luweixuancl/Acode_test/src/web_portal.cpp

#include "web_portal.h"
#include "app_ipc.h"
#include "config.h"
#include "gps_service.h"
#include "ntp_server.h"
#include <ArduinoJson.h>
#include <WiFi.h>
#include <esp_system.h>
#include <math.h>
#include <time.h>

namespace {

String jsonSafeSsid(const String& ssid) {
  const uint8_t* p = reinterpret_cast<const uint8_t*>(ssid.c_str());
  const size_t n = ssid.length();
  bool utf8 = true;
  for (size_t i = 0; i < n;) {
    const uint8_t c = p[i];
    if (c < 0x80) {
      ++i;
      continue;
    }
    size_t need = 0;
    if ((c & 0xE0) == 0xC0) {
      need = 2;
    } else if ((c & 0xF0) == 0xE0) {
      need = 3;
    } else if ((c & 0xF8) == 0xF0) {
      need = 4;
    } else {
      utf8 = false;
      break;
    }
    if (i + need > n) {
      utf8 = false;
      break;
    }
    for (size_t k = 1; k < need; ++k) {
      if ((p[i + k] & 0xC0) != 0x80) {
        utf8 = false;
        break;
      }
    }
    if (!utf8) {
      break;
    }
    i += need;
  }
  if (utf8) {
    return ssid;
  }
  String hex;
  hex.reserve(n * 2 + 4);
  hex = "hex:";
  for (size_t i = 0; i < n; ++i) {
    char b[3];
    snprintf(b, sizeof(b), "%02X", p[i]);
    hex += b;
  }
  return hex;
}

}  // namespace

void WebPortal::begin(WifiManager* wifi, GpsService* gps, NtpServer* ntp) {
  wifi_ = wifi;
  gps_ = gps;
  ntp_ = ntp;
  if (started_) {
    return;
  }

  const char* hdrs[] = {"Cookie"};
  server_.collectHeaders(hdrs, 1);

  server_.on("/", HTTP_GET, [this]() { handleRoot(); });
  server_.on("/setup", HTTP_GET, [this]() { handleSetupEntry(); });
  server_.on("/setup/", HTTP_GET, [this]() { handleSetupEntry(); });
  server_.on("/cfg", HTTP_GET, [this]() { handleSetup(); });
  server_.on("/cfg/", HTTP_GET, [this]() { handleSetup(); });
  server_.on("/login", HTTP_GET, [this]() { sendLoginPage(""); });
  server_.on("/login", HTTP_POST, [this]() { handleLogin(); });
  server_.on("/logout", HTTP_GET, [this]() { handleLogout(); });
  server_.on("/scan", HTTP_GET, [this]() { handleScan(); });
  server_.on("/save", HTTP_POST, [this]() { handleSave(); });
  server_.on("/status", HTTP_GET, [this]() { handleStatus(); });
  server_.on("/metrics", HTTP_GET, [this]() { handleMetrics(); });
  server_.onNotFound([this]() {
    sendNoCache();
    const bool apUp = (WiFi.getMode() == WIFI_AP || WiFi.getMode() == WIFI_AP_STA);
    // Captive probes must not land on settings HTML. SoftAP → login; STA → status.
    if (apUp && wifi_ && !wifi_->isStaConnected()) {
      server_.sendHeader("Location", "/login", true);
      server_.send(302, "text/plain", "");
      return;
    }
    server_.sendHeader("Location", "/", true);
    server_.send(302, "text/plain", "");
  });
  server_.begin();
  started_ = true;
  Serial.println("HTTP on :80  (/ and /status /metrics open; /cfg needs login)");
}

void WebPortal::loop() {
  if (started_) {
    server_.handleClient();
  }
}

bool WebPortal::consumeConnectRequest(String& ssid, String& pass) {
  if (!pendingConnect_) {
    return false;
  }
  pendingConnect_ = false;
  ssid = pendingSsid_;
  pass = pendingPass_;
  return true;
}

String WebPortal::writePassword() const {
  String expect;
  if (settingsLock(pdMS_TO_TICKS(100))) {
    expect = effectiveWebWritePassword(gSettings);
    settingsUnlock();
  } else {
    expect = derivedSoftApPassword();
  }
  if (expect.isEmpty()) {
    expect = derivedSoftApPassword();
  }
  return expect;
}

void WebPortal::sendNoCache() {
  server_.sendHeader("Cache-Control", "no-store, no-cache, must-revalidate, max-age=0");
  server_.sendHeader("Pragma", "no-cache");
}

void WebPortal::issueSession() {
  char tok[17];
  snprintf(tok, sizeof(tok), "%08x%08x", static_cast<unsigned>(esp_random()),
           static_cast<unsigned>(esp_random()));
  sessionToken_ = tok;
  sessionUntilMs_ = millis() + 30UL * 60UL * 1000UL;
  String cookie = String("ntp_sess=") + sessionToken_ +
                  "; Path=/; Max-Age=1800; HttpOnly; SameSite=Lax";
  server_.sendHeader("Set-Cookie", cookie);
}

bool WebPortal::sessionCookieOk() {
  if (sessionToken_.isEmpty() || sessionUntilMs_ == 0) {
    return false;
  }
  if (static_cast<int32_t>(millis() - sessionUntilMs_) >= 0) {
    return false;
  }
  const String cookie = server_.header("Cookie");
  const String needle = String("ntp_sess=") + sessionToken_;
  const int pos = cookie.indexOf(needle);
  if (pos < 0) {
    return false;
  }
  if (pos > 0) {
    const char prev = cookie[pos - 1];
    if (prev != ' ' && prev != ';') {
      return false;
    }
  }
  const int end = pos + needle.length();
  if (end < static_cast<int>(cookie.length())) {
    const char next = cookie[end];
    if (next != ';' && next != ' ') {
      return false;
    }
  }
  return true;
}

bool WebPortal::requireSession(bool htmlLogin) {
  if (sessionCookieOk()) {
    return true;
  }
  if (htmlLogin && server_.method() == HTTP_GET) {
    sendLoginPage("");
    return false;
  }
  sendNoCache();
  server_.send(401, "text/plain", "Unauthorized");
  return false;
}

void WebPortal::sendLoginPage(const char* err) {
  sendNoCache();
  String body;
  body += F("<h1>NTP 设置登录</h1>"
            "<div class='card'>"
            "<p>输入配置口令后才能进入设置。口令默认与 SoftAP 相同"
            "（串口 <code>SoftAP default pass=</code> 或 OLED）。"
            "登录后设置页不再要求填写写口令。</p>");
  if (err && err[0]) {
    body += F("<p class='bad'>");
    body += err;
    body += F("</p>");
  }
  body += F("<form method='POST' action='/login'>"
            "<label>配置口令</label>"
            "<input name='password' type='password' autocomplete='current-password' autofocus>"
            "<button type='submit'>进入设置</button>"
            "</form></div>"
            "<p><a href='/'>返回状态</a></p>");
  server_.send(200, "text/html", buildPage("NTP 登录", body));
}

void WebPortal::handleLogin() {
  const String pass = server_.arg("password");
  const String expect = writePassword();
  if (!pass.isEmpty() && !expect.isEmpty() && pass == expect) {
    issueSession();
    sendNoCache();
    server_.sendHeader("Location", "/cfg", true);
    server_.send(302, "text/plain", "");
    return;
  }
  sendLoginPage("口令错误");
}

void WebPortal::handleLogout() {
  sessionToken_ = "";
  sessionUntilMs_ = 0;
  sendNoCache();
  server_.sendHeader("Set-Cookie", "ntp_sess=; Path=/; Max-Age=0");
  server_.sendHeader("Location", "/login", true);
  server_.send(302, "text/plain", "");
}

void WebPortal::handleSetupEntry() {
  sendNoCache();
  if (sessionCookieOk()) {
    server_.sendHeader("Location", "/cfg", true);
    server_.send(302, "text/plain", "");
    return;
  }
  sendLoginPage("");
}

String WebPortal::buildPage(const String& title, const String& body, bool refresh) const {
  String html;
  html.reserve(body.length() + 700);
  html += F("<!DOCTYPE html><html><head><meta charset='utf-8'>"
            "<meta name='viewport' content='width=device-width,initial-scale=1'>"
            "<meta http-equiv='Cache-Control' content='no-store'>");
  if (refresh) {
    html += F("<meta http-equiv='refresh' content='2'>");
  }
  html += F("<title>");
  html += title;
  html += F("</title><style>"
            "body{font-family:sans-serif;max-width:480px;margin:24px auto;padding:0 12px;background:#0f172a;color:#e2e8f0}"
            "h1{font-size:1.25rem}button,input,select{font-size:1rem;padding:8px;margin:6px 0;width:100%;box-sizing:border-box}"
            "button{background:#38bdf8;border:0;border-radius:8px;color:#0f172a;font-weight:700}"
            "a{color:#38bdf8}.card{background:#1e293b;padding:16px;border-radius:12px;margin:12px 0}"
            ".row{display:flex;justify-content:space-between;gap:12px;padding:6px 0;border-bottom:1px solid #334155}"
            ".row:last-child{border-bottom:0}.k{color:#94a3b8}.v{font-weight:700;text-align:right}"
            ".ok{color:#4ade80}.warn{color:#fbbf24}.bad{color:#f87171}"
            "</style></head><body>");
  html += body;
  html += F("</body></html>");
  return html;
}

void WebPortal::handleRoot() {
  // `/` is always the read-only status page (SoftAP and STA). Settings live at /cfg
  // after login — never serve that HTML here (also busts old cached SoftAP `/` setup).
  sendNoCache();

  // Static shell; live values filled by JS polling /status (no full-page refresh).
  String body = F(
      "<h1>GNSS NTP 状态</h1><p><a href='/cfg'>设置（需登录）</a></p>"
      "<div class='card'>"
      "<div class='row'><span class='k'>NTP</span><span class='v' id='ntpState'>--</span></div>"
      "<div class='row'><span class='k'>时钟</span><span class='v' id='clk'>--</span></div>"
      "<div class='row'><span class='k'>Residual</span><span class='v' id='res'>--</span></div>"
      "<div class='row'><span class='k'>频偏</span><span class='v' id='freq'>--</span></div>"
      "<div class='row'><span class='k'>Root 质量</span><span class='v' id='qual'>--</span></div>"
      "<div class='row'><span class='k'>策略</span><span class='v' id='apol'>--</span></div>"
      "<div class='row'><span class='k'>守时上限</span><span class='v' id='hold'>--</span></div>"
      "<div class='row'><span class='k'>守时中</span><span class='v' id='holdms'>--</span></div>"
      "<div class='row'><span class='k'>Stratum</span><span class='v' id='stratum'>--</span></div>"
      "<div class='row'><span class='k'>Leap</span><span class='v' id='li'>--</span></div>"
      "<div class='row'><span class='k'>RefID</span><span class='v' id='refId'>GPSS</span></div>"
      "<div class='row'><span class='k'>查询次数</span><span class='v' id='ntpReq'>--</span></div>"
      "<div class='row'><span class='k'>UTC</span><span class='v' id='utc'>--</span></div>"
      "<div class='row'><span class='k'>本地</span><span class='v' id='local'>--</span></div>"
      "</div>"
      "<div class='card'>"
      "<div class='row'><span class='k'>GPS 锁定</span><span class='v' id='fix'>--</span></div>"
      "<div class='row'><span class='k'>搜星</span><span class='v' id='sats'>--</span></div>"
      "<div class='row'><span class='k'>HDOP</span><span class='v' id='hdop'>--</span></div>"
      "<div class='row'><span class='k'>PPS</span><span class='v' id='pps'>--</span></div>"
      "<div class='row'><span class='k'>NMEA 龄</span><span class='v' id='age'>--</span></div>"
      "<div class='row'><span class='k'>时间有效</span><span class='v' id='tvalid'>--</span></div>"
      "<div class='row'><span class='k'>经纬度</span><span class='v' id='ll'>--</span></div>"
      "</div>"
      "<div class='card'>"
      "<div class='row'><span class='k'>已服务</span><span class='v' id='served'>--</span></div>"
      "<div class='row'><span class='k'>限流 RATE</span><span class='v' id='rate'>--</span></div>"
      "<div class='row'><span class='k'>DENY</span><span class='v' id='deny'>--</span></div>"
      "<div class='row'><span class='k'>静默丢弃</span><span class='v' id='drop'>--</span></div>"
      "<div class='row'><span class='k'>ACL 拒绝</span><span class='v' id='adny'>--</span></div>"
      "<div class='row'><span class='k'>活跃客户端</span><span class='v' id='clients'>--</span></div>"
      "<div class='row'><span class='k'>ACL 模式</span><span class='v' id='aclm'>--</span></div>"
      "</div>"
      "<div class='card'>"
      "<div class='row'><span class='k'>IP</span><span class='v' id='ip'>--</span></div>"
      "<div class='row'><span class='k'>SSID</span><span class='v' id='ssid'>--</span></div>"
      "<div class='row'><span class='k'>RSSI</span><span class='v' id='rssi'>--</span></div>"
      "<div class='row'><span class='k'>MAC</span><span class='v' id='mac'>--</span></div>"
      "<div class='row'><span class='k'>运行</span><span class='v' id='up'>--</span></div>"
      "<div class='row'><span class='k'>内存</span><span class='v' id='heap'>--</span></div>"
      "<div class='row'><span class='k'>温度</span><span class='v' id='temp'>--</span></div>"
      "</div>"
      "<p style='color:#64748b'>自动更新 1 Hz · JSON: <a href='/status'>/status</a> · 指标: <a href='/metrics'>/metrics</a></p>"
      "<script>"
      "function pad(n){return n<10?'0'+n:''+n}"
      "function fmt(epoch,tz){"
      " if(!epoch)return '--';"
      " const d=new Date((epoch+tz*3600)*1000);"
      " return d.getUTCFullYear()+'-'+pad(d.getUTCMonth()+1)+'-'+pad(d.getUTCDate())+' '"
      "  +pad(d.getUTCHours())+':'+pad(d.getUTCMinutes())+':'+pad(d.getUTCSeconds())}"
      "function fmtUp(s){"
      " if(s==null)return '--';"
      " const d=Math.floor(s/86400),h=Math.floor(s%86400/3600),m=Math.floor(s%3600/60),x=s%60;"
      " return (d?d+'d ':'')+pad(h)+':'+pad(m)+':'+pad(x)}"
      "function setCls(el,c){el.className='v '+(c||'')}"
      "async function tick(){"
      " try{"
      "  const r=await fetch('/status'); const j=await r.json();"
      "  const g=j.gps||{}, n=j.ntp||{}, c=j.clock||{};"
      "  const have=!!n.synced, pps=!!g.ppsFresh, s1=!!n.stratum1Ready;"
      "  const st=document.getElementById('ntpState');"
      "  st.textContent=s1?'Stratum 1 就绪':(have?'降级/守时':'未同步');"
      "  setCls(st,s1?'ok':(have?'warn':'bad'));"
      "  document.getElementById('clk').textContent=c.state||'--';"
      "  document.getElementById('res').textContent=(c.residualMs!=null)?(c.residualMs+' ms'):'--';"
      "  document.getElementById('freq').textContent=(c.freqPpm!=null)"
      "    ?(Number(c.freqPpm).toFixed(2)+' ppm'):'--';"
      "  document.getElementById('qual').textContent=(g.qualityMs!=null)?(g.qualityMs+' ms'):'--';"
      "  document.getElementById('apol').textContent=j.anomalyLabel||'--';"
      "  document.getElementById('hold').textContent=(j.holdoverSec!=null)?(j.holdoverSec+' s'):'--';"
      "  const hm=document.getElementById('holdms');"
      "  hm.textContent=(c.holdoverMs>0)?(Math.round(c.holdoverMs/1000)+' s'):'-';"
      "  setCls(hm,c.holdoverMs>0?'warn':'');"
      "  document.getElementById('stratum').textContent=(n.stratum!=null)?n.stratum:'--';"
      "  const li=document.getElementById('li');"
      "  li.textContent=(n.li!=null)?('LI='+n.li):'--'; setCls(li,n.li===0?'ok':'warn');"
      "  document.getElementById('refId').textContent=n.refId||'GPSS';"
      "  document.getElementById('ntpReq').textContent=(n.requests!=null)?n.requests:'--';"
      "  const tz=j.tzHours||0;"
      "  document.getElementById('utc').textContent=fmt(g.utcEpoch,0);"
      "  document.getElementById('local').textContent=fmt(g.utcEpoch,tz)"
      "    +' (UTC'+(tz>=0?'+':'')+tz+')';"
      "  const fx=document.getElementById('fix');"
      "  fx.textContent=g.fix?'是':'否'; setCls(fx,g.fix?'ok':'bad');"
      "  document.getElementById('sats').textContent=(g.satellites!=null)?g.satellites:'--';"
      "  document.getElementById('hdop').textContent=(g.hdop!=null)?Number(g.hdop).toFixed(1):'--';"
      "  const pp=document.getElementById('pps');"
      "  pp.textContent=(pps?'正常':'无')+' ('+(g.ppsCount||0)+')'; setCls(pp,pps?'ok':'bad');"
      "  document.getElementById('age').textContent=(g.ageMs!=null)?(g.ageMs+' ms'):'--';"
      "  const tv=document.getElementById('tvalid');"
      "  tv.textContent=g.timeValid?'有效':'无效'; setCls(tv,g.timeValid?'ok':'bad');"
      "  document.getElementById('ll').textContent=g.fix"
      "    ?(Number(g.lat).toFixed(5)+', '+Number(g.lon).toFixed(5)):'--';"
      "  document.getElementById('served').textContent=(n.served!=null)?n.served:'--';"
      "  document.getElementById('rate').textContent=(n.rateLimited!=null)?n.rateLimited:'--';"
      "  document.getElementById('deny').textContent=(n.denied!=null)?n.denied:'--';"
      "  document.getElementById('drop').textContent=(n.dropped!=null)?n.dropped:'--';"
      "  document.getElementById('adny').textContent=(n.aclDenied!=null)?n.aclDenied:'--';"
      "  document.getElementById('clients').textContent=(n.clients!=null)?n.clients:'--';"
      "  document.getElementById('aclm').textContent=(j.ntpAclLabel||'--')"
      "    +' ('+((j.ntpAcl&&j.ntpAcl.length)||0)+')';"
      "  document.getElementById('ip').textContent=j.ip||'--';"
      "  document.getElementById('ssid').textContent=j.ssid||'--';"
      "  document.getElementById('rssi').textContent=(j.rssi!=null)?(j.rssi+' dBm'):'--';"
      "  document.getElementById('mac').textContent=j.mac||'--';"
      "  document.getElementById('up').textContent=fmtUp(j.uptimeSec);"
      "  const hb=Math.round((j.freeHeap||0)/1024), hmn=Math.round((j.minFreeHeap||0)/1024);"
      "  const he=document.getElementById('heap');"
      "  he.textContent=hb+' KB (min '+hmn+')'; setCls(he,hb<20480?'bad':'');"
      "  const tp=document.getElementById('temp');"
      "  tp.textContent=(c.tempC!=null)?(Number(c.tempC).toFixed(1)+'°C · '"
      "    +(c.tempComp?('补偿 '+Number(c.tempCorrPpm||0).toFixed(2)+' ppm'):'补偿关')):'--';"
      " }catch(e){}"
      "}"
      "tick(); setInterval(tick,1000);"
      "</script>");

  server_.send(200, "text/html", buildPage("NTP 状态", body, false));
}

void WebPortal::handleSetup() {
  if (!requireSession(true)) {
    return;
  }
  uint8_t apol = 0;
  uint8_t aclm = 0;
  bool tcmp = false;
  int16_t tcpc = CLK_TEMP_COEFF_CENTI;
  uint32_t ooffMin = OLED_IDLE_OFF_DEFAULT_MS / 60000;
  String aclLines;
  String savedSsid;
  bool haveSaved = false;
  if (settingsLock(pdMS_TO_TICKS(50))) {
    apol = static_cast<uint8_t>(gSettings.anomalyPolicy);
    aclm = static_cast<uint8_t>(gSettings.ntpAclMode);
    tcmp = gSettings.tempComp;
    tcpc = gSettings.tempCoeffCenti;
    ooffMin = gSettings.oledIdleOffMs / 60000;
    for (uint8_t i = 0; i < gSettings.ntpAclCount && i < NTP_ACL_MAX_ENTRIES; ++i) {
      if (i) {
        aclLines += '\n';
      }
      aclLines += gSettings.ntpAcl[i].toString();
    }
    savedSsid = gSettings.wifiSsid;
    haveSaved = !savedSsid.isEmpty();
    settingsUnlock();
  }
  String body;
  body.reserve(5600);
  body += F("<!-- ntp-cfg-v2 -->"
            "<h1>NTP 设置</h1><p><a href='/'>返回状态</a> · <a href='/logout'>退出</a></p>");
  if (haveSaved) {
    body += F("<div class='card'><h2 style='font-size:1rem;margin:0 0 8px'>已保存的 WiFi</h2><p>SSID: <b>");
    body += savedSsid;
    body += F("</b></p>"
              "<p style='color:#64748b;font-size:.85rem'>固件更新后会自动重连；无需重新输入 WiFi 密码。"
              "仅当路由器改密或换热点时才需要下方重新配网。</p>"
              "<button type='button' onclick='reconnectSaved()'>使用已保存网络重连</button>"
              "<p id='rmsg'></p></div>");
  }
  body += F("<div class='card'><h2 style='font-size:1rem;margin:0 0 8px'>GPS 异常策略</h2>"
            "<select id='apol'>"
            "<option value='0'>立即拒绝授时 (Refuse)</option>"
            "<option value='1'>短时守时 Holdover 30s</option>"
            "<option value='2'>长时守时 Holdover 5min</option>"
            "</select>"
            "<button type='button' onclick='savePolicy()'>保存策略</button>"
            "<p id='pmsg'></p></div>");
  body += F("<div class='card'><h2 style='font-size:1rem;margin:0 0 8px'>NTP ACL 白名单</h2>"
            "<p style='color:#64748b;font-size:.85rem'>默认 Off。开启 AllowList 后仅列出的 IPv4 可取时"
            "（最多 8 条；未命中静默丢弃；空列表=拒绝全部）。</p>"
            "<label>模式</label><select id='aclm'>"
            "<option value='0'>Off（不限制）</option>"
            "<option value='1'>AllowList</option>"
            "</select>"
            "<label>允许的 IP（每行一个）</label>"
            "<textarea id='acllist' rows='5' style='width:100%;font-family:monospace'></textarea>"
            "<button type='button' onclick='saveAcl()'>保存 ACL</button>"
            "<p id='amsg'></p></div>");
  body += F("<div class='card'><h2 style='font-size:1rem;margin:0 0 8px'>晶振温度补偿</h2>"
            "<p style='color:#64748b;font-size:.85rem'>默认关。用片上温度对 Holdover 外推做一阶 "
            "ppm/°C 修正（相对最近 PPS 估频时的温度）。系数可改，默认 -0.50。</p>"
            "<label>模式</label><select id='tcmp'>"
            "<option value='0'>Off</option>"
            "<option value='1'>On</option>"
            "</select>"
            "<label>系数 ppm/°C</label>"
            "<input id='tcpc' type='number' step='0.01'>"
            "<button type='button' onclick='saveTemp()'>保存温度补偿</button>"
            "<p id='tmsg'></p></div>");
  body += F("<div class='card'><h2 style='font-size:1rem;margin:0 0 8px'>屏幕息屏</h2>"
            "<p style='color:#64748b;font-size:.85rem'>无旋钮操作达到该时长后关闭 OLED 面板（防烧屏）。"
            "旋转/单击旋钮唤醒，首个动作仅唤醒不导航；系统提示（OK IP 等）会自动亮屏。0 = 常亮。</p>"
            "<label>息屏时间</label><select id='ooff'>"
            "<option value='0'>常亮（不息屏）</option>"
            "<option value='1'>1 分钟</option>"
            "<option value='5'>5 分钟</option>"
            "<option value='10'>10 分钟（默认）</option>"
            "<option value='30'>30 分钟</option>"
            "</select>"
            "<button type='button' onclick='saveScreen()'>保存息屏</button>"
            "<p id='smsg'></p></div>");
  body += F("<div class='card'><h2 style='font-size:1rem;margin:0 0 8px'>WiFi 配网</h2>"
            "<p>扫描热点，选择 SSID，输入密码后连接。</p>"
            "<button type='button' onclick='scan()'>扫描 WiFi</button>"
            "<label>SSID</label><select id='ssid'></select>"
            "<label>Password</label><input id='pass' type='password'>"
            "<button type='button' onclick='saveWifi()'>连接</button>"
            "<p id='msg'></p></div>");
  body += F("<script>"
            "async function sleep(ms){return new Promise(r=>setTimeout(r,ms));}"
            "async function postSave(obj){"
            " const r=await fetch('/save',{method:'POST',credentials:'same-origin',"
            "  headers:{'Content-Type':'application/json'},body:JSON.stringify(obj)});"
            " if(r.status===401){location.href='/login';return '';}"
            " return r.text();}"
            "async function scan(){"
            " try{"
            " document.getElementById('msg').textContent='Scanning...';"
            " let j=null;"
            " for(let i=0;i<50;i++){"
            "  const r=await fetch('/scan',{credentials:'same-origin'});"
            "  if(r.status===401){location.href='/login';return;}"
            "  if(r.status===202){await sleep(250);continue;}"
            "  if(!r.ok){document.getElementById('msg').textContent='Scan failed';return;}"
            "  j=await r.json(); break;"
            " }"
            " if(!j){document.getElementById('msg').textContent='Scan timeout';return;}"
            " const s=document.getElementById('ssid'); s.innerHTML='';"
            " j.forEach(n=>{const o=document.createElement('option');"
            " o.value=n.ssid; o.textContent=n.ssid+' ('+n.rssi+'dBm)'; s.appendChild(o);});"
            " document.getElementById('msg').textContent='Found '+j.length+' networks';"
            " }catch(e){document.getElementById('msg').textContent=String(e);}"
            "}"
            "async function saveWifi(){"
            " try{"
            " const ssid=document.getElementById('ssid').value;"
            " const pass=document.getElementById('pass').value;"
            " document.getElementById('msg').textContent=await postSave({ssid,pass});"
            " }catch(e){document.getElementById('msg').textContent=String(e);}"
            "}"
            "async function reconnectSaved(){"
            " try{"
            "  document.getElementById('rmsg').textContent=await postSave({reconnectSaved:true});"
            " }catch(e){document.getElementById('rmsg').textContent=String(e);}"
            "}"
            "async function savePolicy(){"
            " try{"
            " const anomalyPolicy=parseInt(document.getElementById('apol').value,10);"
            " document.getElementById('pmsg').textContent=await postSave({anomalyPolicy});"
            " }catch(e){document.getElementById('pmsg').textContent=String(e);}"
            "}"
            "async function saveAcl(){"
            " try{"
            " const ntpAclMode=parseInt(document.getElementById('aclm').value,10);"
            " const ntpAcl=document.getElementById('acllist').value.split(/\\r?\\n/)"
            "  .map(s=>s.trim()).filter(s=>s.length>0);"
            " document.getElementById('amsg').textContent=await postSave({ntpAclMode,ntpAcl});"
            " }catch(e){document.getElementById('amsg').textContent=String(e);}"
            "}"
            "async function saveTemp(){"
            " try{"
            " const tempComp=parseInt(document.getElementById('tcmp').value,10)===1;"
            " const tempCoeff=parseFloat(document.getElementById('tcpc').value);"
            " document.getElementById('tmsg').textContent=await postSave({tempComp,tempCoeff});"
            " }catch(e){document.getElementById('tmsg').textContent=String(e);}"
            "}"
            "async function saveScreen(){"
            " try{"
            " const oledIdleMin=parseInt(document.getElementById('ooff').value,10);"
            " document.getElementById('smsg').textContent=await postSave({oledIdleMin});"
            " }catch(e){document.getElementById('smsg').textContent=String(e);}"
            "}"
            "document.getElementById('apol').value='");
  body += String(apol);
  body += F("';"
            "document.getElementById('aclm').value='");
  body += String(aclm);
  body += F("';"
            "document.getElementById('tcmp').value='");
  body += String(tcmp ? 1 : 0);
  body += F("';"
            "document.getElementById('tcpc').value='");
  {
    char buf[16];
    snprintf(buf, sizeof(buf), "%.2f", static_cast<double>(tempCoeffPpmPerC(tcpc)));
    body += buf;
  }
  body += F("';"
            "document.getElementById('ooff').value='");
  body += String(static_cast<unsigned>(ooffMin));
  body += F("';"
            "document.getElementById('acllist').value=");
  // JSON-encode the ACL lines for safe JS string.
  {
    JsonDocument tmp;
    tmp.set(aclLines);
    String enc;
    serializeJson(tmp, enc);
    body += enc;
  }
  body += F(";");
  if (!haveSaved) {
    body += F("scan();");
  }
  body += F("</script>");
  sendNoCache();
  server_.send(200, "text/html", buildPage("NTP 设置", body));
}

void WebPortal::handleScan() {
  if (!requireSession(false)) {
    return;
  }
  if (wifi_ == nullptr) {
    server_.send(503, "application/json", "{\"error\":\"no wifi\"}");
    return;
  }

  // Do not kick STA join or scanDelete() an in-flight OLED harvest.
  if (wifi_->isConnecting() && !wifi_->isStaConnected()) {
    server_.send(202, "application/json", "{\"status\":\"scanning\"}");
    return;
  }
  const bool cacheFresh =
      wifi_->scanState() == WifiScanState::Done && !wifi_->lastScan().empty() &&
      static_cast<int32_t>(millis() - wifi_->lastHarvestMs()) < WIFI_SCAN_CACHE_MS;
  if (!wifi_->isScanRunning() && !wifi_->peekScanDone() && !cacheFresh) {
    if (!wifi_->startScan()) {
      server_.send(503, "application/json", "{\"status\":\"busy\"}");
      return;
    }
  }

  std::vector<WifiNetwork> nets;
  const WifiScanState st = wifi_->pollScan(&nets);
  if (st == WifiScanState::Running) {
    server_.send(202, "application/json", "{\"status\":\"scanning\"}");
    return;
  }
  if (st == WifiScanState::Failed) {
    server_.send(500, "application/json", "{\"status\":\"failed\"}");
    return;
  }

  const std::vector<WifiNetwork>& src = nets.empty() ? wifi_->lastScan() : nets;

  JsonDocument doc;
  JsonArray arr = doc.to<JsonArray>();
  for (const auto& n : src) {
    JsonObject o = arr.add<JsonObject>();
    o["ssid"] = jsonSafeSsid(n.ssid);
    o["rssi"] = n.rssi;
  }
  String out;
  serializeJson(doc, out);
  server_.send(200, "application/json", out);
}

void WebPortal::handleSave() {
  if (!requireSession(false)) {
    return;
  }
  String body = server_.arg("plain");
  JsonDocument doc;
  if (deserializeJson(doc, body)) {
    server_.send(400, "text/plain", "Bad JSON");
    return;
  }

  // Optional password overrides (still require auth above).
  bool touchMgmt = false;
  if (doc["apPassword"].is<const char*>()) {
    String ap = doc["apPassword"].as<const char*>();
    if (ap == "null") {
      ap = "";
    }
    if (!ap.isEmpty() && ap.length() < 8) {
      server_.send(400, "text/plain", "apPassword must be >=8 chars");
      return;
    }
    if (settingsLock(pdMS_TO_TICKS(100))) {
      gSettings.apPassword = ap;
      settingsUnlock();
      touchMgmt = true;
    }
  }
  if (doc["webPassword"].is<const char*>()) {
    String wp = doc["webPassword"].as<const char*>();
    if (wp == "null") {
      wp = "";
    }
    if (settingsLock(pdMS_TO_TICKS(100))) {
      gSettings.webPassword = wp;
      settingsUnlock();
      touchMgmt = true;
    }
  }
  if (touchMgmt && settingsLock(pdMS_TO_TICKS(100))) {
    AppSettings copy = gSettings;
    settingsUnlock();
    gStore.save(copy);
  }

  // Reuse NVS WiFi without retyping password (SoftAP escape / post-OTA).
  if (doc["reconnectSaved"] == true) {
    String ssid;
    String pass;
    if (settingsLock(pdMS_TO_TICKS(200))) {
      ssid = gSettings.wifiSsid;
      pass = gSettings.wifiPass;
      settingsUnlock();
    }
    if (ssid.isEmpty()) {
      server_.send(400, "text/plain", "No saved WiFi");
      return;
    }
    pendingSsid_ = ssid;
    pendingPass_ = pass;
    pendingConnect_ = true;
    server_.send(200, "text/plain", "Reconnecting with saved WiFi...");
    return;
  }

  bool savedPolicy = false;
  if (!doc["anomalyPolicy"].isNull()) {
    const int v = doc["anomalyPolicy"].as<int>();
    if (v >= 0 && v <= static_cast<int>(AnomalyPolicy::HoldoverLong)) {
      AppSettings copy;
      bool locked = false;
      if (settingsLock(pdMS_TO_TICKS(200))) {
        gSettings.anomalyPolicy = static_cast<AnomalyPolicy>(v);
        const uint16_t defHold = anomalyPolicyDefaultHoldoverSec(gSettings.anomalyPolicy);
        if (defHold > 0) {
          gSettings.holdoverSec = defHold;
        }
        if (!doc["holdoverSec"].isNull()) {
          uint16_t hs = doc["holdoverSec"].as<uint16_t>();
          if (hs < 10) hs = 10;
          if (hs > 600) hs = 600;
          gSettings.holdoverSec = hs;
        }
        copy = gSettings;
        settingsUnlock();
        locked = true;
      }
      if (locked) {
        gStore.save(copy);
        savedPolicy = true;
      }
    }
  }

  bool savedAcl = false;
  const bool haveAclMode = !doc["ntpAclMode"].isNull();
  const bool haveAclList = doc["ntpAcl"].is<JsonArray>();
  if (haveAclMode || haveAclList) {
    AppSettings copy;
    bool locked = false;
    if (settingsLock(pdMS_TO_TICKS(200))) {
      if (haveAclMode) {
        const int m = doc["ntpAclMode"].as<int>();
        gSettings.ntpAclMode =
            (m == static_cast<int>(NtpAclMode::AllowList)) ? NtpAclMode::AllowList : NtpAclMode::Off;
      }
      if (haveAclList) {
        JsonArray arr = doc["ntpAcl"].as<JsonArray>();
        uint8_t n = 0;
        for (JsonVariant v : arr) {
          if (n >= NTP_ACL_MAX_ENTRIES) {
            break;
          }
          if (!v.is<const char*>()) {
            continue;
          }
          IPAddress ip;
          if (ip.fromString(v.as<const char*>()) && static_cast<uint32_t>(ip) != 0) {
            gSettings.ntpAcl[n++] = ip;
          }
        }
        gSettings.ntpAclCount = n;
      }
      copy = gSettings;
      settingsUnlock();
      locked = true;
    }
    if (locked) {
      gStore.save(copy);
      savedAcl = true;
    }
  }

  bool savedTemp = false;
  const bool haveTempComp = !doc["tempComp"].isNull();
  const bool haveTempCoeff = !doc["tempCoeff"].isNull();
  if (haveTempComp || haveTempCoeff) {
    AppSettings copy;
    bool locked = false;
    if (settingsLock(pdMS_TO_TICKS(200))) {
      if (haveTempComp) {
        gSettings.tempComp = doc["tempComp"].as<bool>();
      }
      if (haveTempCoeff) {
        float k = doc["tempCoeff"].as<float>();
        if (k < -5.0f) {
          k = -5.0f;
        }
        if (k > 5.0f) {
          k = 5.0f;
        }
        gSettings.tempCoeffCenti = static_cast<int16_t>(lroundf(k * 100.0f));
      }
      copy = gSettings;
      settingsUnlock();
      locked = true;
    }
    if (locked) {
      gStore.save(copy);
      savedTemp = true;
    }
  }

  // OLED idle blanking timeout, in whole minutes (0 = always on).
  bool savedScreen = false;
  if (!doc["oledIdleMin"].isNull()) {
    uint32_t mins = doc["oledIdleMin"].as<uint32_t>();
    if (mins > 60) {
      mins = 60;
    }
    AppSettings copy;
    bool locked = false;
    if (settingsLock(pdMS_TO_TICKS(200))) {
      gSettings.oledIdleOffMs = mins * 60000UL;
      copy = gSettings;
      settingsUnlock();
      locked = true;
    }
    if (locked) {
      gStore.save(copy);
      savedScreen = true;
    }
  }

  // Only touch WiFi creds when ssid is a real JSON string (not missing/null).
  if (doc["ssid"].is<const char*>()) {
    pendingSsid_ = doc["ssid"].as<const char*>();
    pendingPass_ = doc["pass"].is<const char*>() ? String(doc["pass"].as<const char*>()) : String();
    if (pendingSsid_ == "null" || pendingSsid_ == "undefined") {
      pendingSsid_ = "";
    }
    if (!pendingSsid_.isEmpty()) {
      AppSettings copy;
      bool locked = false;
      if (settingsLock(pdMS_TO_TICKS(200))) {
        gSettings.wifiSsid = pendingSsid_;
        gSettings.wifiPass = pendingPass_;
        copy = gSettings;
        settingsUnlock();
        locked = true;
      }
      if (locked) {
        gStore.save(copy);
      }
      pendingConnect_ = true;
      server_.send(200, "text/plain", "Saved. Connecting...");
      return;
    }
  }

  if (savedPolicy || touchMgmt || savedAcl || savedTemp || savedScreen) {
    if (savedTemp) {
      server_.send(200, "text/plain", "Temp comp saved");
    } else if (savedScreen) {
      server_.send(200, "text/plain", "Screen timeout saved");
    } else if (savedAcl) {
      server_.send(200, "text/plain", "ACL saved");
    } else {
      server_.send(200, "text/plain", savedPolicy ? "Policy saved" : "Password updated");
    }
    return;
  }
  server_.send(400, "text/plain", "SSID or anomalyPolicy or ntpAcl required");
}

void WebPortal::handleStatus() {
  JsonDocument doc;
  doc["sta"] = wifi_->isStaConnected();
  doc["ip"] = wifi_->localIp().toString();
  doc["ssid"] = WiFi.SSID();
  doc["rssi"] = WiFi.RSSI();
  doc["mac"] = wifi_->macAddress();
  doc["uptimeSec"] = millis() / 1000;
  doc["freeHeap"] = ESP.getFreeHeap();
  doc["minFreeHeap"] = ESP.getMinFreeHeap();

  AnomalyPolicy apol = AnomalyPolicy::Refuse;
  uint16_t hold = 0;
  String savedSsid;
  NtpAclMode aclMode = NtpAclMode::Off;
  uint8_t aclCount = 0;
  bool tcmp = false;
  int16_t tcpc = CLK_TEMP_COEFF_CENTI;
  IPAddress aclIps[NTP_ACL_MAX_ENTRIES];
  if (settingsLock(pdMS_TO_TICKS(20))) {
    doc["tzHours"] = gSettings.timezoneHours;
    apol = gSettings.anomalyPolicy;
    hold = gSettings.holdoverSec;
    savedSsid = gSettings.wifiSsid;
    tcmp = gSettings.tempComp;
    tcpc = gSettings.tempCoeffCenti;
    aclMode = gSettings.ntpAclMode;
    aclCount = gSettings.ntpAclCount;
    if (aclCount > NTP_ACL_MAX_ENTRIES) {
      aclCount = NTP_ACL_MAX_ENTRIES;
    }
    for (uint8_t i = 0; i < aclCount; ++i) {
      aclIps[i] = gSettings.ntpAcl[i];
    }
    settingsUnlock();
  } else {
    doc["tzHours"] = 8;
  }
  doc["anomalyPolicy"] = static_cast<uint8_t>(apol);
  doc["anomalyLabel"] = anomalyPolicyMenuLabel(apol);
  doc["holdoverSec"] = hold;
  doc["savedSsid"] = savedSsid;
  doc["hasSavedWifi"] = !savedSsid.isEmpty();
  doc["ntpAclMode"] = static_cast<uint8_t>(aclMode);
  doc["ntpAclLabel"] = ntpAclModeMenuLabel(aclMode);
  doc["tempComp"] = tcmp;
  doc["tempCoeff"] = tempCoeffPpmPerC(tcpc);
  {
    JsonArray arr = doc["ntpAcl"].to<JsonArray>();
    for (uint8_t i = 0; i < aclCount; ++i) {
      arr.add(aclIps[i].toString());
    }
  }

  const GpsStatus st = gps_ ? gps_->snapshot() : GpsStatus{};
  JsonObject gps = doc["gps"].to<JsonObject>();
  gps["fix"] = st.validFix;
  gps["satellites"] = st.satellites;
  gps["hdop"] = st.hdop;
  gps["lat"] = st.lat;
  gps["lon"] = st.lon;
  gps["ppsFresh"] = st.ppsFresh;
  gps["ppsCount"] = st.ppsCount;
  gps["utcEpoch"] = st.utcEpoch;
  gps["ageMs"] = st.ageMs;
  gps["timeValid"] = st.timeValid;
  gps["qualityMs"] = st.qualityMs;

  JsonObject clock = doc["clock"].to<JsonObject>();
  clock["state"] = clockStateLabel(st.clockState);
  clock["stateCode"] = static_cast<uint8_t>(st.clockState);
  clock["residualMs"] = st.residualMs;
  clock["freqPpm"] = st.freqPpm;
  clock["tempC"] = st.tempC;
  clock["tempCorrPpm"] = st.tempCorrPpm;
  clock["tempComp"] = st.tempComp;
  clock["holdoverMs"] = st.holdoverMs;

  JsonObject ntp = doc["ntp"].to<JsonObject>();
  const bool syncOk = st.timeValid && (st.clockState == ClockState::Locked ||
                                       st.clockState == ClockState::Degraded ||
                                       st.clockState == ClockState::Holdover);
  ntp["synced"] = syncOk;
  ntp["stratum"] = syncOk ? 1 : 16;
  ntp["stratum1Ready"] = st.timeValid && st.clockState == ClockState::Locked && st.ppsFresh;
  ntp["refId"] = syncOk ? "GPSS" : "INIT";
  // LI is leap-second indicator only; holdover stays LI=0 with rising dispersion.
  ntp["li"] = syncOk ? 0 : 3;
  ntp["requests"] = ntp_ ? ntp_->requestCount() : 0;
  ntp["served"] = ntp_ ? ntp_->servedCount() : 0;
  ntp["rateLimited"] = ntp_ ? ntp_->rateLimitedCount() : 0;
  ntp["denied"] = ntp_ ? ntp_->deniedCount() : 0;
  ntp["dropped"] = ntp_ ? ntp_->droppedCount() : 0;
  ntp["aclDenied"] = ntp_ ? ntp_->aclDeniedCount() : 0;
  ntp["clients"] = ntp_ ? ntp_->activeClientCount() : 0;

  String out;
  serializeJson(doc, out);
  sendNoCache();
  server_.send(200, "application/json", out);
}

void WebPortal::handleMetrics() {
  // Prometheus-ish text; no auth (read-only, same as /status).
  char buf[640];
  const uint32_t served = ntp_ ? ntp_->servedCount() : 0;
  const uint32_t rate = ntp_ ? ntp_->rateLimitedCount() : 0;
  const uint32_t denied = ntp_ ? ntp_->deniedCount() : 0;
  const uint32_t dropped = ntp_ ? ntp_->droppedCount() : 0;
  const uint32_t aclDenied = ntp_ ? ntp_->aclDeniedCount() : 0;
  const uint32_t reqs = ntp_ ? ntp_->requestCount() : 0;
  const uint8_t clients = ntp_ ? ntp_->activeClientCount() : 0;
  const unsigned heap = ESP.getFreeHeap();
  const unsigned aclMode = ntp_ ? static_cast<unsigned>(ntp_->aclMode()) : 0;
  const unsigned aclCount = ntp_ ? ntp_->aclCount() : 0;
  snprintf(buf, sizeof(buf),
           "# TYPE ntp_requests_total counter\n"
           "ntp_requests_total %lu\n"
           "# TYPE ntp_served_total counter\n"
           "ntp_served_total %lu\n"
           "# TYPE ntp_rate_limited_total counter\n"
           "ntp_rate_limited_total %lu\n"
           "# TYPE ntp_denied_total counter\n"
           "ntp_denied_total %lu\n"
           "# TYPE ntp_dropped_total counter\n"
           "ntp_dropped_total %lu\n"
           "# TYPE ntp_acl_denied_total counter\n"
           "ntp_acl_denied_total %lu\n"
           "# TYPE ntp_acl_mode gauge\n"
           "ntp_acl_mode %u\n"
           "# TYPE ntp_acl_entries gauge\n"
           "ntp_acl_entries %u\n"
           "# TYPE ntp_clients gauge\n"
           "ntp_clients %u\n"
           "# TYPE esp_free_heap_bytes gauge\n"
           "esp_free_heap_bytes %u\n",
           static_cast<unsigned long>(reqs), static_cast<unsigned long>(served),
           static_cast<unsigned long>(rate), static_cast<unsigned long>(denied),
           static_cast<unsigned long>(dropped), static_cast<unsigned long>(aclDenied), aclMode,
           aclCount, static_cast<unsigned>(clients), heap);
  server_.send(200, "text/plain; charset=utf-8", buf);
}
