luweixuancl/Acode_test/src/gps_service.cpp

#include "gps_service.h"
#include <esp_timer.h>
#include "driver/temp_sensor.h"

portMUX_TYPE GpsService::ppsMux_ = portMUX_INITIALIZER_UNLOCKED;
volatile uint32_t GpsService::ppsCount_ = 0;
volatile uint64_t GpsService::ppsLastEdgeUs_ = 0;
volatile uint8_t GpsService::ppsQHead_ = 0;
volatile uint8_t GpsService::ppsQTail_ = 0;
volatile GpsService::PpsIsrEdge GpsService::ppsQ_[GPS_PPS_ISR_QUEUE] = {};
TaskHandle_t GpsService::timeTask_ = nullptr;

void IRAM_ATTR GpsService::onPpsIsr() {
  const uint64_t edgeUs = esp_timer_get_time();
  portENTER_CRITICAL_ISR(&ppsMux_);
  const uint32_t count = ++ppsCount_;
  ppsLastEdgeUs_ = edgeUs;

  const uint8_t next = static_cast<uint8_t>((ppsQHead_ + 1) % GPS_PPS_ISR_QUEUE);
  if (next == ppsQTail_) {
    // Drop oldest so newest edges survive under load.
    ppsQTail_ = static_cast<uint8_t>((ppsQTail_ + 1) % GPS_PPS_ISR_QUEUE);
  }
  ppsQ_[ppsQHead_].edgeUs = edgeUs;
  ppsQ_[ppsQHead_].count = count;
  ppsQHead_ = next;
  portEXIT_CRITICAL_ISR(&ppsMux_);

  BaseType_t woken = pdFALSE;
  if (timeTask_ != nullptr) {
    vTaskNotifyGiveFromISR(timeTask_, &woken);
  }
  if (woken) {
    portYIELD_FROM_ISR();
  }
}

void GpsService::begin() {
  localClock_.reset();
  pinMode(PIN_GPS_PPS, INPUT_PULLDOWN);
  gpsSerial_.setRxBufferSize(2048);
  gpsSerial_.begin(GPS_UART_BAUD, SERIAL_8N1, PIN_GPS_RX, PIN_GPS_TX);
  attachInterrupt(digitalPinToInterrupt(PIN_GPS_PPS), onPpsIsr, RISING);
  {
    temp_sensor_config_t tsens = TSENS_CONFIG_DEFAULT();
    temp_sensor_set_config(tsens);
    const esp_err_t err = temp_sensor_start();
    tempSensorOk_ = (err == ESP_OK || err == ESP_ERR_INVALID_STATE);
    Serial.printf("GPS UART%d RX=%d TX=%d baud=%d buf=2048 local-clock=on ppsQ=%d tsens=%d\n",
                  GPS_UART_NUM, PIN_GPS_RX, PIN_GPS_TX, GPS_UART_BAUD, GPS_PPS_ISR_QUEUE,
                  tempSensorOk_ ? 1 : 0);
  }
}

void GpsService::setTempComp(bool enabled, int16_t coeffCenti) {
  localClock_.setTempComp(enabled, coeffCenti);
}

void GpsService::sampleDieTemp() {
  if (!tempSensorOk_) {
    return;
  }
  const uint32_t now = millis();
  if (lastTempMs_ != 0 && (now - lastTempMs_) < CLK_TEMP_SAMPLE_MS) {
    return;
  }
  lastTempMs_ = now;
  float c = NAN;
  if (temp_sensor_read_celsius(&c) == ESP_OK) {
    localClock_.updateDieTemp(c);
  }
}

void GpsService::loop(AnomalyPolicy policy, uint16_t holdoverSec) {
  sampleDieTemp();
  parseNmea();

  // Drain every queued PPS edge (WiFi may delay task-time by >1s).
  uint32_t drainedCount = 0;
  for (;;) {
    uint64_t edgeUs = 0;
    uint32_t count = 0;
    bool got = false;
    portENTER_CRITICAL(&ppsMux_);
    if (ppsQTail_ != ppsQHead_) {
      edgeUs = ppsQ_[ppsQTail_].edgeUs;
      count = ppsQ_[ppsQTail_].count;
      ppsQTail_ = static_cast<uint8_t>((ppsQTail_ + 1) % GPS_PPS_ISR_QUEUE);
      got = true;
    }
    portEXIT_CRITICAL(&ppsMux_);
    if (!got) {
      break;
    }
    ppsSeen_ = true;
    drainedCount = count;
    localClock_.onPpsEdge(edgeUs, count);
  }
  if (drainedCount != 0) {
    lastDrainedPpsCount_ = drainedCount;
  }

  GpsStatus work;
  work.satellites = gps_.satellites.isValid() ? gps_.satellites.value() : 0;
  // isValid() alone is sticky after first fix; require recent updates and sats>0 so
  // antenna-loss (0 sats / stale NMEA) clears "GPS 锁定" on OLED/Web.
  const bool locFresh =
      gps_.location.isValid() && gps_.location.age() <= GPS_FIX_MAX_AGE_MS;
  const bool timeFresh = gps_.date.isValid() && gps_.time.isValid() &&
                         gps_.time.age() <= GPS_FIX_MAX_AGE_MS;
  const bool satsOk = gps_.satellites.isValid() &&
                      gps_.satellites.age() <= GPS_FIX_MAX_AGE_MS && work.satellites > 0;
  work.validFix = locFresh && timeFresh && satsOk;
  if (locFresh) {
    work.lat = gps_.location.lat();
    work.lon = gps_.location.lng();
  }
  if (gps_.hdop.isValid() && gps_.hdop.age() <= GPS_FIX_MAX_AGE_MS) {
    work.hdop = gps_.hdop.hdop();
  }
  work.ppsSeen = ppsSeen_;
  work.ppsCount = ppsCount_;
  work.ppsFresh = ppsFresh();

  if (gps_.date.isValid() && gps_.time.isValid()) {
    TinyGPSDate d = gps_.date;
    TinyGPSTime t = gps_.time;
    int y = d.year();
    int m = d.month();
    int day = d.day();
    if (m <= 2) {
      y -= 1;
      m += 12;
    }
    int64_t a = y / 100;
    int64_t b = 2 - a + a / 4;
    int64_t jd = static_cast<int64_t>(365.25 * (y + 4716)) +
                 static_cast<int64_t>(30.6001 * (m + 1)) + day + b - 1524;
    int64_t daysSinceUnix = jd - 2440588;
    const uint32_t epoch = static_cast<uint32_t>(daysSinceUnix * 86400LL + t.hour() * 3600L +
                                                 t.minute() * 60L + t.second());
    work.ageMs = gps_.time.age();
    if (epoch != lastCommittedSecond_) {
      commitNmeaTime(epoch, policy, holdoverSec);
      lastCommittedSecond_ = epoch;
    }
  } else {
    work.ageMs = 0xFFFFFFFF;
  }

  const bool nmeaFresh = haveCommit_ && (millis() - commitMs_) <= 3000;
  localClock_.tick(nmeaFresh, work.ppsFresh, policy, holdoverSec);

  work.qualityMs = qualityMs();
  uint32_t sec = 0;
  uint32_t frac = 0;
  work.timeValid = nowUtc(sec, frac);
  work.utcEpoch = work.timeValid ? sec : commitEpoch_;
  work.clockState = localClock_.state();
  work.residualMs = localClock_.residualMs();
  work.freqPpm = localClock_.freqPpm();
  work.tempC = localClock_.dieTempC();
  work.tempCorrPpm = localClock_.tempCorrPpm();
  work.tempComp = localClock_.tempCompEnabled();
  work.holdoverMs = localClock_.holdoverElapsedMs();

  publishStatus(work);

#if GPS_DEBUG
  const uint32_t now = millis();
  if (now - lastDebugMs_ >= 1000) {
    lastDebugMs_ = now;
    Serial.printf(
        "GPS fix=%d sat=%u pps=%u utc=%lu valid=%d clk=%s r=%ld ppm=%.1f q=%lu hold=%lu\n",
        work.validFix ? 1 : 0, work.satellites, work.ppsCount,
        static_cast<unsigned long>(work.utcEpoch), work.timeValid ? 1 : 0,
        clockStateLabel(work.clockState), static_cast<long>(work.residualMs),
        static_cast<double>(work.freqPpm), static_cast<unsigned long>(work.qualityMs),
        static_cast<unsigned long>(work.holdoverMs));
  }
#endif
}

void GpsService::commitNmeaTime(uint32_t epochSec, AnomalyPolicy policy, uint16_t holdoverSec) {
  commitEpoch_ = epochSec;
  commitPpsCount_ = lastDrainedPpsCount_ != 0 ? lastDrainedPpsCount_ : ppsCount_;
  commitMs_ = millis();
  haveCommit_ = true;
  localClock_.onNmeaCommit(epochSec, commitPpsCount_, policy, holdoverSec);
}

void GpsService::publishStatus(const GpsStatus& work) {
  portENTER_CRITICAL(&mux_);
  published_ = work;
  portEXIT_CRITICAL(&mux_);
}

void GpsService::parseNmea() {
  int budget = GPS_NMEA_MAX_BYTES_PER_LOOP;
  while (budget-- > 0 && gpsSerial_.available() > 0) {
    const char c = static_cast<char>(gpsSerial_.read());
#if GPS_DEBUG_NMEA
    Serial.write(c);
#endif
    gps_.encode(c);
  }
}

GpsStatus GpsService::snapshot() const {
  GpsStatus out;
  portENTER_CRITICAL(&mux_);
  out = published_;
  portEXIT_CRITICAL(&mux_);
  return out;
}

bool GpsService::ppsFresh() const {
  uint64_t edge = 0;
  portENTER_CRITICAL(&ppsMux_);
  edge = ppsLastEdgeUs_;
  portEXIT_CRITICAL(&ppsMux_);
  if (edge == 0) {
    return false;
  }
  const uint64_t now = esp_timer_get_time();
  return (now >= edge) && ((now - edge) < 1500000ULL);
}

uint32_t GpsService::qualityMs() const {
  return localClock_.qualityMs();
}

bool GpsService::nowUtc(uint32_t& seconds, uint32_t& fraction) const {
  // NTP honesty: only LocalClock Locked/Degraded/Holdover may serve time.
  return localClock_.nowUtc(seconds, fraction);
}

bool GpsService::referenceUtc(uint32_t& seconds, uint32_t& fraction) const {
  return localClock_.referenceUtc(seconds, fraction);
}
