luweixuancl/Acode_test/include/app_ipc.h

#pragma once

#include <Arduino.h>
#include <IPAddress.h>
#include <vector>
#include <freertos/FreeRTOS.h>
#include <freertos/queue.h>
#include <freertos/semphr.h>
#include "settings.h"
#include "wifi_manager.h"

// Cross-task IPC for RTOS refactor (time / net / ui).

enum class NetReqType : uint8_t {
  ConnectWifi,
  ScanWifi,
  ApplyStaticIp,
  UseDhcp,
  StartWebSetup,
};

struct NetRequest {
  NetReqType type = NetReqType::ConnectWifi;
  char ssid[33] = {};
  char pass[65] = {};
  IPAddress staticIp;
  uint32_t seq = 0;  // OLED scan generation; 0 = unspecified
};

enum class UiMsgType : uint8_t {
  Text,
  ScanResult,
  ScanFailed,
};

struct UiMsg {
  UiMsgType type = UiMsgType::Text;
  char text[48] = {};
  uint32_t seq = 0;  // must match DisplayUi scanSeq_ for ScanResult/ScanFailed
  // Scan results: payload lives in shared scan buffer guarded by scanMutex.
};

struct AppIpc {
  QueueHandle_t netReq = nullptr;
  QueueHandle_t uiMsg = nullptr;
  SemaphoreHandle_t settingsMutex = nullptr;
  SemaphoreHandle_t scanMutex = nullptr;
  std::vector<WifiNetwork> scanResults;
  bool scanReady = false;
  bool setupAp = false;

  // Task liveness stamps (millis); StatusLeds panics if any go stale.
  volatile uint32_t kickTimeMs = 0;
  volatile uint32_t kickNetMs = 0;
  volatile uint32_t kickUiMs = 0;
};

extern AppIpc gIpc;
extern AppSettings gSettings;
extern SettingsStore gStore;

bool ipcInit();
bool settingsLock(TickType_t ticks);
void settingsUnlock();
bool postNetRequest(const NetRequest& req);
bool postUiText(const char* text);

inline void ipcKickTime() { gIpc.kickTimeMs = millis(); }
inline void ipcKickNet() { gIpc.kickNetMs = millis(); }
inline void ipcKickUi() { gIpc.kickUiMs = millis(); }
